MickiusMousius/Rolio46Keyboard/pcb/right/3D Models/pg1350-mbk.step

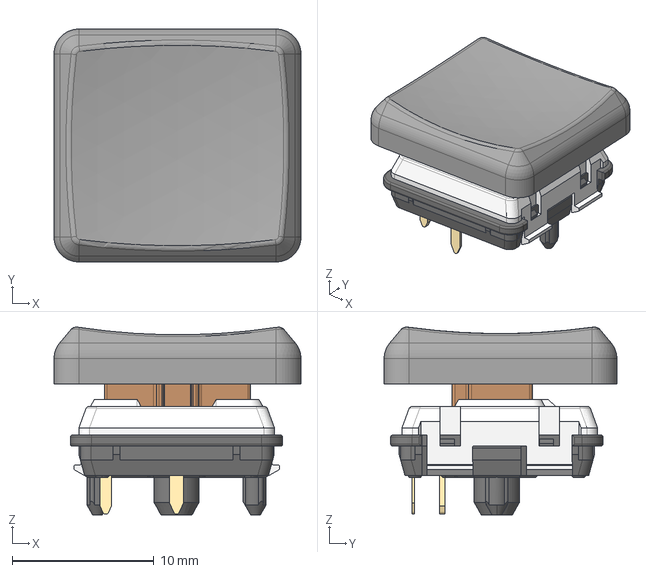
[picture p33: CAD file, 2023-09-10]
pcb/right/3D Models/pg1350-mbk.step
17.4 x 16.4 x 13.3 mm
(Unsaved)
Document x 5
